MakerM0/PixelTime/software/font3x8.py

FONT3X8 = (
# 
# NUM0 =
(
    1, 1, 1,
    1, 0, 1,
    1, 0, 1,
    1, 0, 1,
    1, 0, 1,
    1, 0, 1,
    1, 0, 1,
    1, 1, 1,
),
# 
# NUM1 =
    (
    0, 1, 0,
    1, 1, 0,
    0, 1, 0,
    0, 1, 0,
    0, 1, 0,
    0, 1, 0,
    0, 1, 0,
    1, 1, 1,
),
# 
# NUM2 =
    (
    1, 1, 1,
    0, 0, 1,
    0, 0, 1,
    1, 1, 1,
    1, 0, 0,
    1, 0, 0,
    1, 0, 0,
    1, 1, 1,
),
# 
# NUM3 =
(
    1, 1, 1,
    0, 0, 1,
    0, 0, 1,
    1, 1, 1,
    0, 0, 1,
    0, 0, 1,
    0, 0, 1,
    1, 1, 1,
),
# 
# NUM4 =
(
    1, 0, 1,
    1, 0, 1,
    1, 0, 1,
    1, 1, 1,
    0, 0, 1,
    0, 0, 1,
    0, 0, 1,
    0, 0, 1,
),
# 
# NUM5 =
(
    1, 1, 1,
    1, 0, 0,
    1, 0, 0,
    1, 1, 1,
    0, 0, 1,
    0, 0, 1,
    0, 0, 1,
    1, 1, 1,
),
# 
# NUM6 =
    (
    1, 1, 1,
    1, 0, 0,
    1, 0, 0,
    1, 1, 1,
    1, 0, 1,
    1, 0, 1,
    1, 0, 1,
    1, 1, 1,
),
# 
# NUM7 =
    (
    1, 1, 1,
    0, 0, 1,
    0, 0, 1,
    0, 0, 1,
    0, 0, 1,
    0, 0, 1,
    0, 0, 1,
    0, 0, 1,
),
# 
# NUM8 =
    (
    1, 1, 1,
    1, 0, 1,
    1, 0, 1,
    1, 1, 1,
    1, 0, 1,
    1, 0, 1,
    1, 0, 1,
    1, 1, 1,
),
# 
# NUM9 =
    (
    1, 1, 1,
    1, 0, 1,
    1, 0, 1,
    1, 1, 1,
    0, 0, 1,
    0, 0, 1,
    0, 0, 1,
    1, 1, 1,
)
)
