MakerM0/PixelTime/software/week7x7.py

WEEK7X8=(
    (0,1,1,1,1,1,0,
     0,1,0,0,0,1,0,
     0,1,0,0,0,1,0,
     0,1,1,1,1,1,0,
     0,1,0,0,0,1,0,
     0,1,0,0,0,1,0,
     0,1,1,1,1,1,0,
     0,0,0,0,0,0,0,
 
     ),#日
    (0,0,0,0,0,0,0,
     0,0,0,0,0,0,0,
     0,0,0,0,0,1,0,
     1,1,1,1,1,1,1,
     0,0,0,0,0,0,0,
     0,0,0,0,0,0,0,
     0,0,0,0,0,0,0,
     0,0,0,0,0,0,0,

     ),#一
    (
     0,0,0,0,0,0,0,
     0,1,1,1,1,1,0,
     0,0,0,0,0,0,0,
     0,0,0,0,0,0,0,
     0,0,0,0,0,0,0,
     0,0,0,0,0,1,0,  
     1,1,1,1,1,1,1,
     0,0,0,0,0,0,0,
    
     ),#二
    (0,0,0,0,0,0,0,
     0,1,1,1,1,1,0,
     0,0,0,0,0,0,0,
     0,0,1,1,1,0,0,
     0,0,0,0,0,0,0,
     0,0,0,0,0,0,0,
     1,1,1,1,1,1,1,
     0,0,0,0,0,0,0,
 
     ),#三
    ( 
     1,1,1,1,1,1,1,
     1,0,1,0,1,0,1,
     1,0,1,0,1,0,1,
     1,0,1,0,1,1,1,
     1,1,0,0,0,0,1,
     1,0,0,0,0,0,1,
     1,1,1,1,1,1,1,
     0,0,0,0,0,0,0,
     ),#四
    ( 
     0,1,1,1,1,1,0,
     0,0,0,1,0,0,0,
     0,0,0,1,0,0,0,
     0,1,1,1,1,1,0,
     0,0,1,0,0,1,0,
     0,0,1,0,0,1,0,  
     1,1,1,1,1,1,1,
     0,0,0,0,0,0,0,
      
     ),#五
    ( 
     0,0,0,1,0,0,0,
     1,1,1,1,1,1,1,
     0,0,0,0,0,0,0,
     0,0,1,0,1,0,0,
     0,0,1,0,1,0,0,
     0,1,0,0,0,1,0,
     1,0,0,0,0,0,1,
     0,0,0,0,0,0,0,
     ),#六
    ( 
     0,1,1,1,1,1,1,
     0,1,0,1,0,0,1,
     0,1,1,1,1,0,1,
     0,1,0,1,0,0,1,
     0,1,1,1,1,1,1,
     0,1,1,0,1,0,1,
     1,0,1,1,1,0,1,
     0,0,0,0,0,0,0,
     ),#周
    
    
    )
